marfikus/3d-kinematics/3d_models/parts/table_2_stepper_holder.SLDPRT

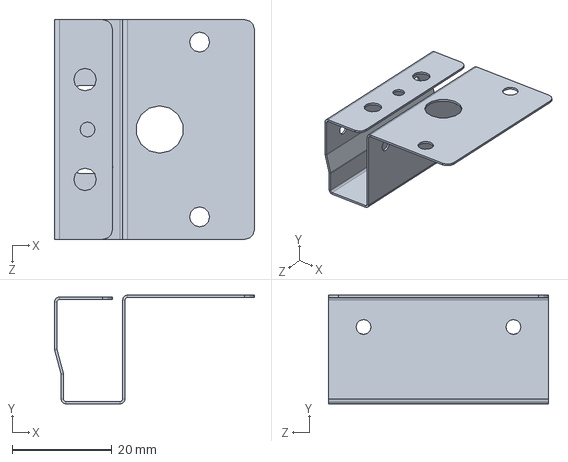
[picture p17: CAD file, 2021-09-27]
3d_models/parts/table_2_stepper_holder.SLDPRT
40.1 x 21.8 x 44.0 mm
