marfikus/3d-kinematics/3d_models/parts/z_axis_side_support.SLDPRT

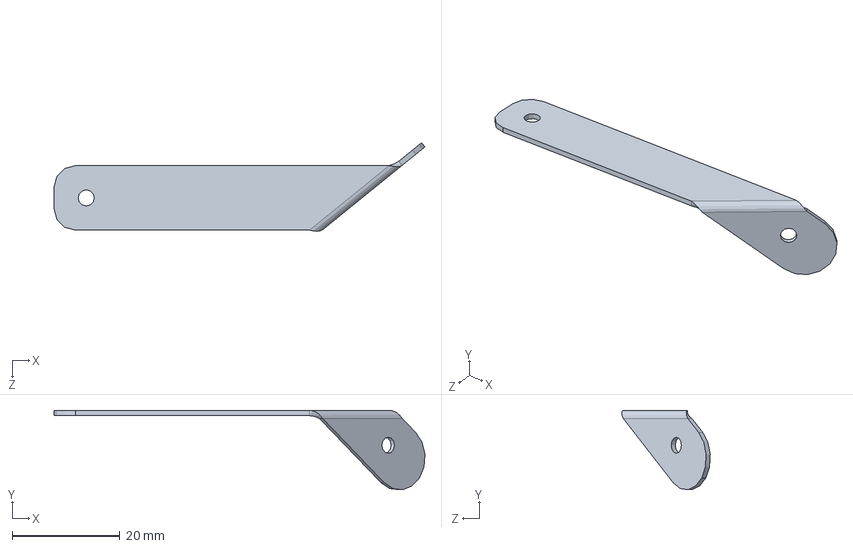
[picture p18: CAD file, 2021-09-27]
3d_models/parts/z_axis_side_support.SLDPRT
69.0 x 14.8 x 16.5 mm
