marfikus/3d-kinematics/3d_models/parts/table_2_stepper_rail_support_right.SLDPRT

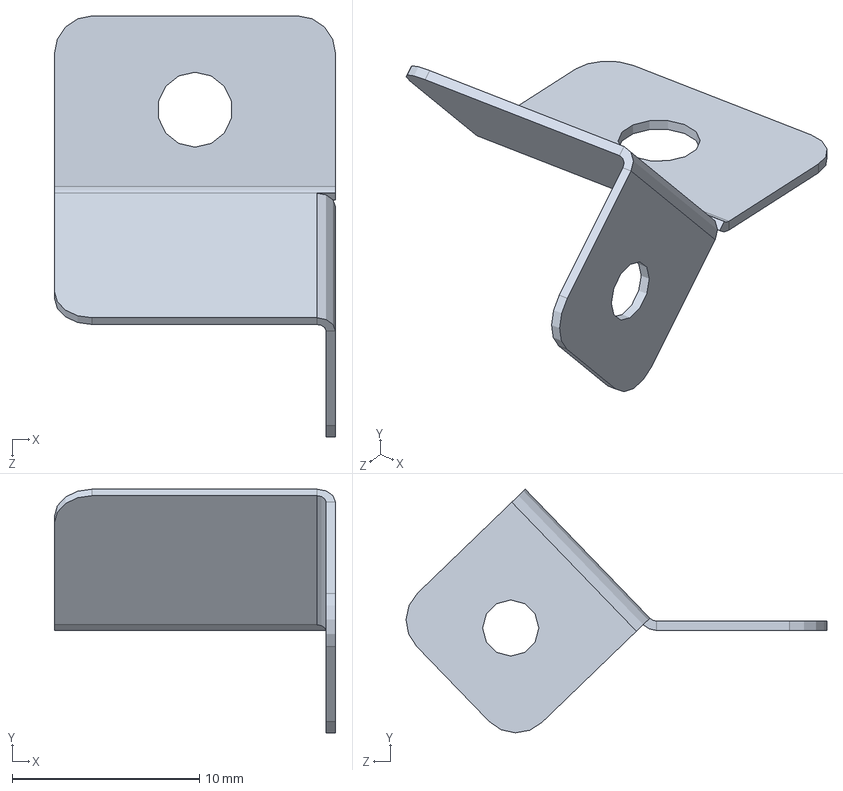
[picture p19: CAD file, 2021-09-27]
3d_models/parts/table_2_stepper_rail_support_right.SLDPRT
15.0 x 13.0 x 22.5 mm
