marfikus/3d-kinematics/3d_models/parts/table_1_stepper_holder.SLDPRT

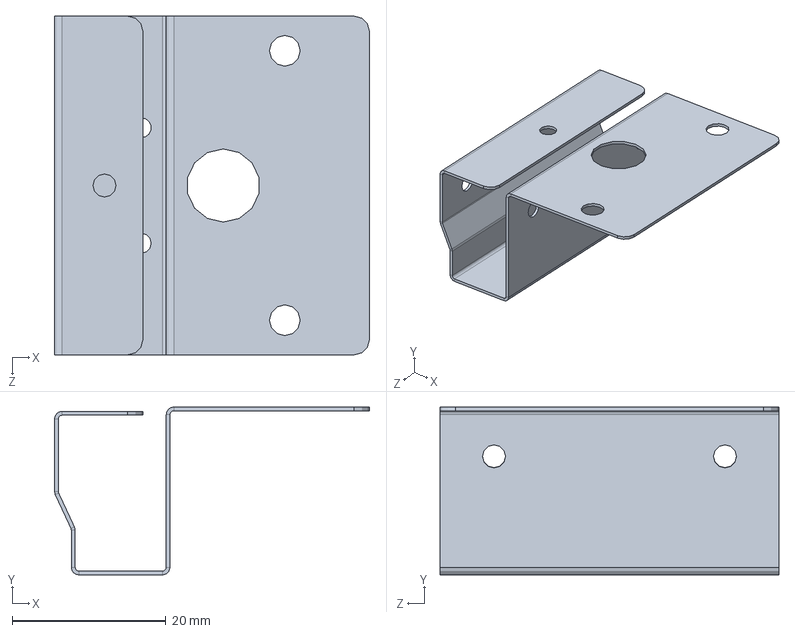
[picture p20: CAD file, 2021-09-27]
3d_models/parts/table_1_stepper_holder.SLDPRT
40.9 x 21.8 x 44.0 mm
