marfikus/3d-kinematics/3d_models/parts/z_axis_stepper_holder.SLDPRT

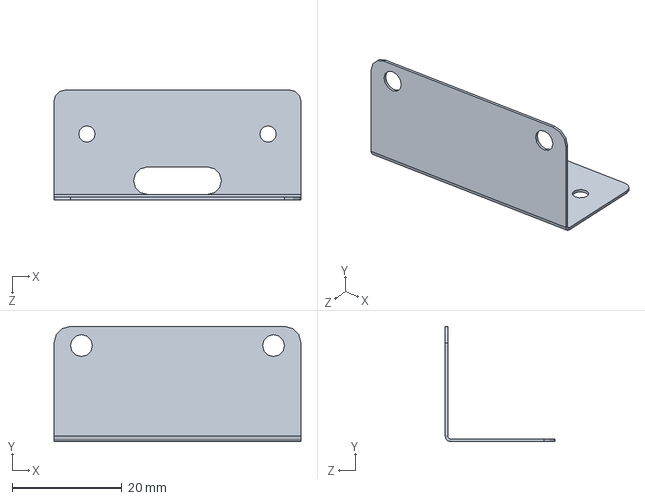
[picture p21: CAD file, 2021-09-27]
3d_models/parts/z_axis_stepper_holder.SLDPRT
45.0 x 21.0 x 20.0 mm
