marfikus/3d-kinematics/3d_models/parts/z_axis_rails_holder_1_2.SLDPRT

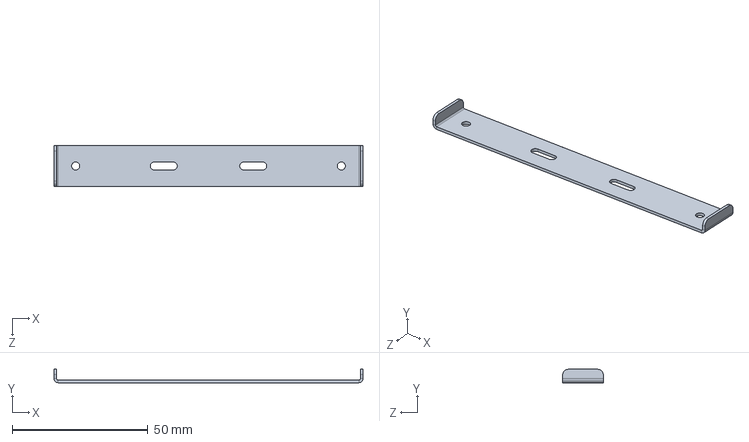
[picture p22: CAD file, 2021-09-27]
3d_models/parts/z_axis_rails_holder_1_2.SLDPRT
114.0 x 5.00 x 15.0 mm
