marfikus/3d-kinematics/3d_models/parts/table_support_1.SLDPRT

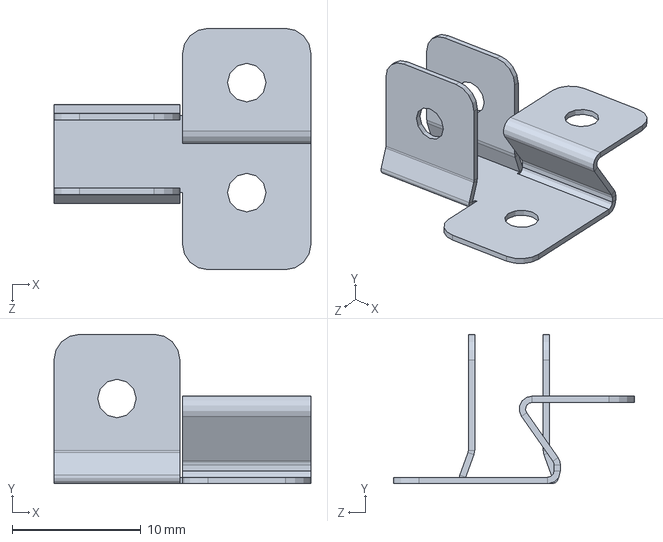
[picture p23: CAD file, 2021-09-24]
3d_models/parts/table_support_1.SLDPRT
20.0 x 11.6 x 18.8 mm
