marfikus/3d-kinematics/3d_models/parts/table_1_rail_support.SLDPRT

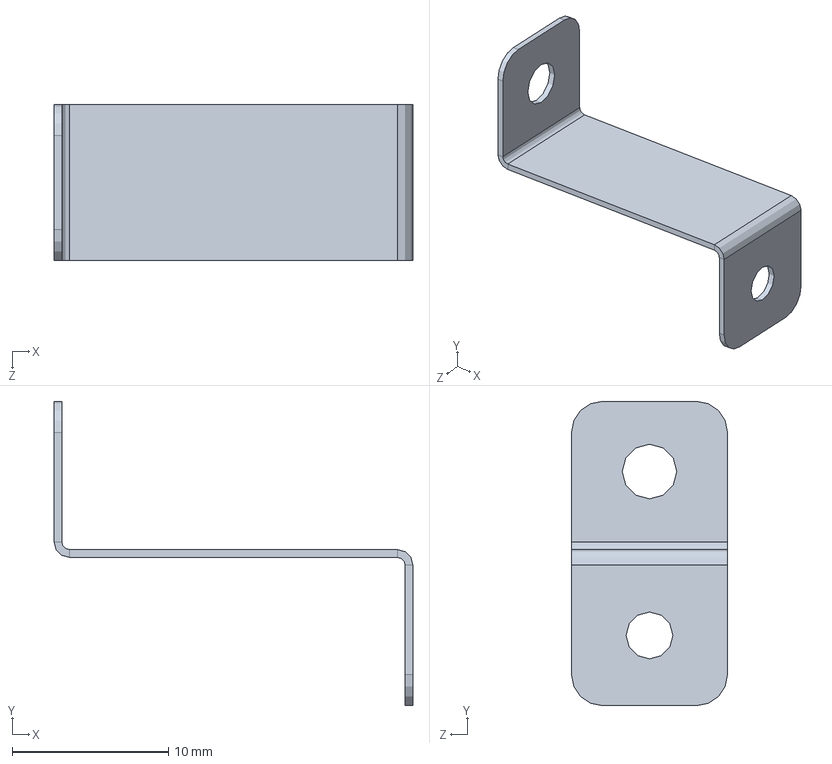
[picture p24: CAD file, 2021-09-24]
3d_models/parts/table_1_rail_support.SLDPRT
23.0 x 19.5 x 10.0 mm
