marfikus/3d-kinematics/3d_models/parts/table_1.SLDPRT

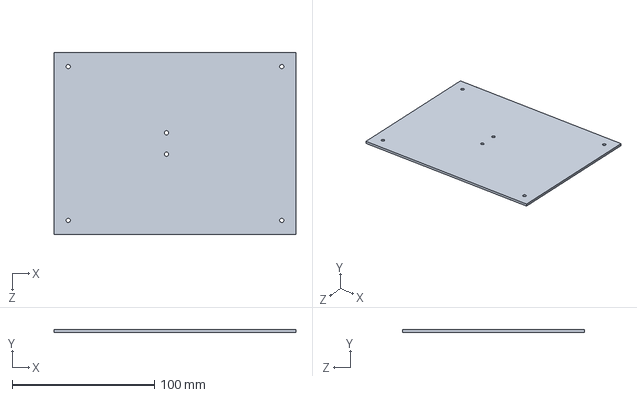
[picture p25: CAD file, 2021-09-24]
3d_models/parts/table_1.SLDPRT
170.0 x 2.00 x 128.0 mm
