marfikus/3d-kinematics/3d_models/parts/table_1_stepper_rail_support.SLDPRT

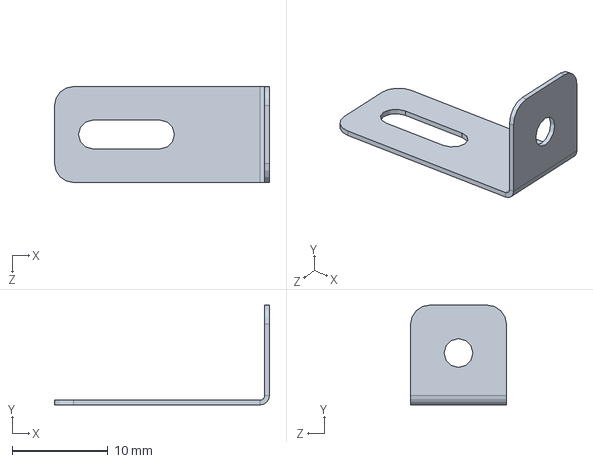
[picture p26: CAD file, 2021-09-24]
3d_models/parts/table_1_stepper_rail_support.SLDPRT
22.4 x 10.4 x 10.0 mm
