marfikus/3d-kinematics/3d_models/parts/table_support_2.SLDPRT

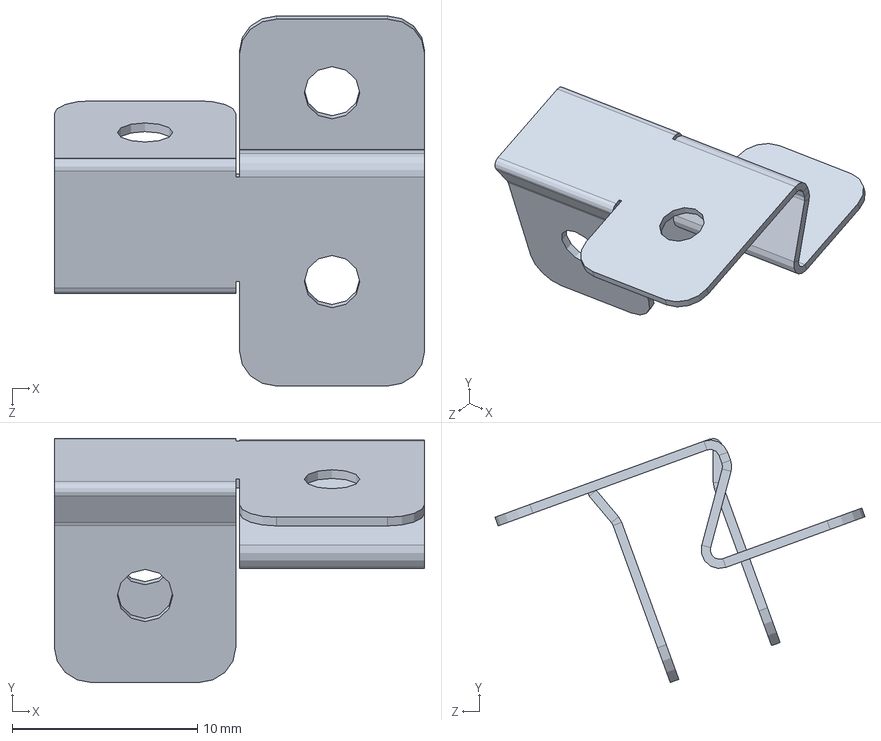
[picture p27: CAD file, 2021-09-24]
3d_models/parts/table_support_2.SLDPRT
20.0 x 13.2 x 20.0 mm
