marfikus/3d-kinematics/3d_models/parts/z_axis_rack_bracing_1_1.SLDPRT

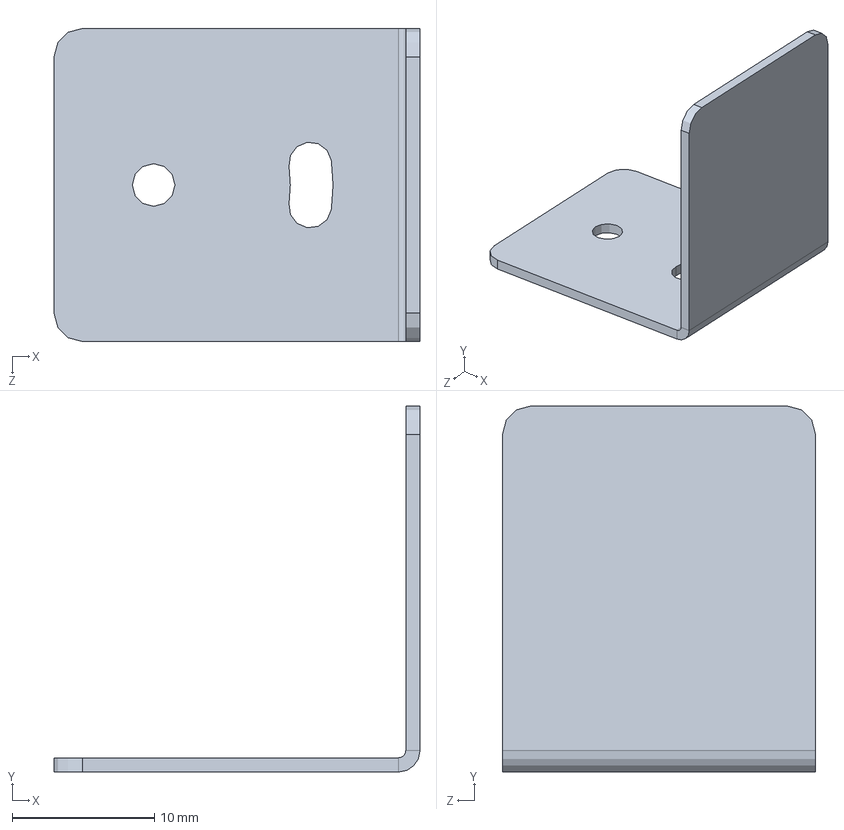
[picture p28: CAD file, 2021-09-23]
3d_models/parts/z_axis_rack_bracing_1_1.SLDPRT
25.7 x 25.7 x 22.0 mm
