marfikus/3d-kinematics/3d_models/parts/z_axis_rack_bracing_1_2.SLDPRT

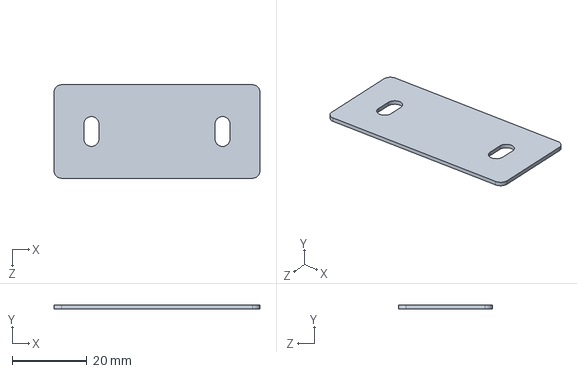
[picture p29: CAD file, 2021-09-23]
3d_models/parts/z_axis_rack_bracing_1_2.SLDPRT
55.0 x 1.00 x 25.0 mm
