marfikus/3d-kinematics/3d_models/parts/z_axis_upper_corner.SLDPRT

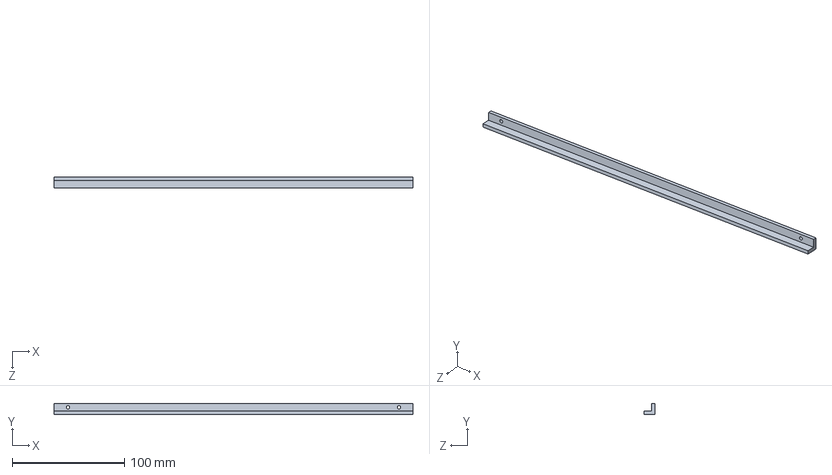
[picture p30: CAD file, 2021-09-23]
3d_models/parts/z_axis_upper_corner.SLDPRT
320.0 x 10.0 x 10.0 mm
