marfikus/3d-kinematics/3d_models/parts/base.SLDPRT

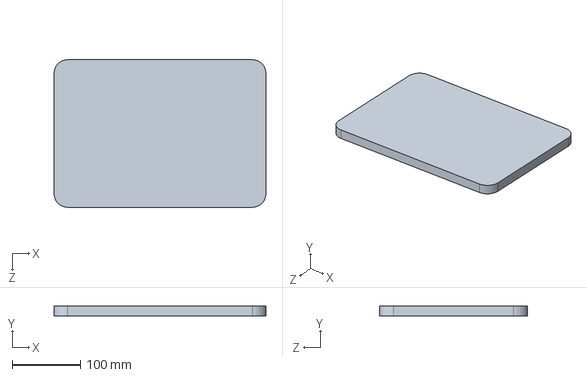
[picture p31: CAD file, 2021-09-21]
3d_models/parts/base.SLDPRT
310.0 x 15.0 x 216.0 mm
