marfikus/3d-kinematics/3d_models/parts/corner_rail_2.SLDPRT

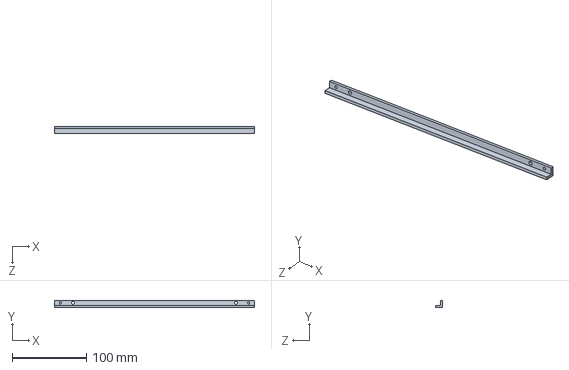
[picture p32: CAD file, 2021-09-21]
3d_models/parts/corner_rail_2.SLDPRT
270.0 x 10.0 x 10.0 mm
