marfikus/3d-kinematics/3d_models/parts/corner_rail_3.SLDPRT

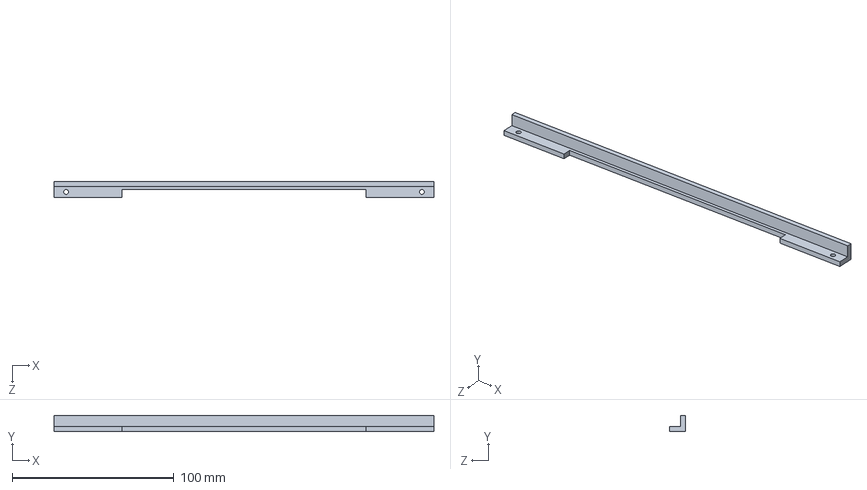
[picture p33: CAD file, 2021-09-21]
3d_models/parts/corner_rail_3.SLDPRT
235.0 x 10.0 x 10.0 mm
