marfikus/3d-kinematics/3d_models/parts/short_roller.SLDPRT

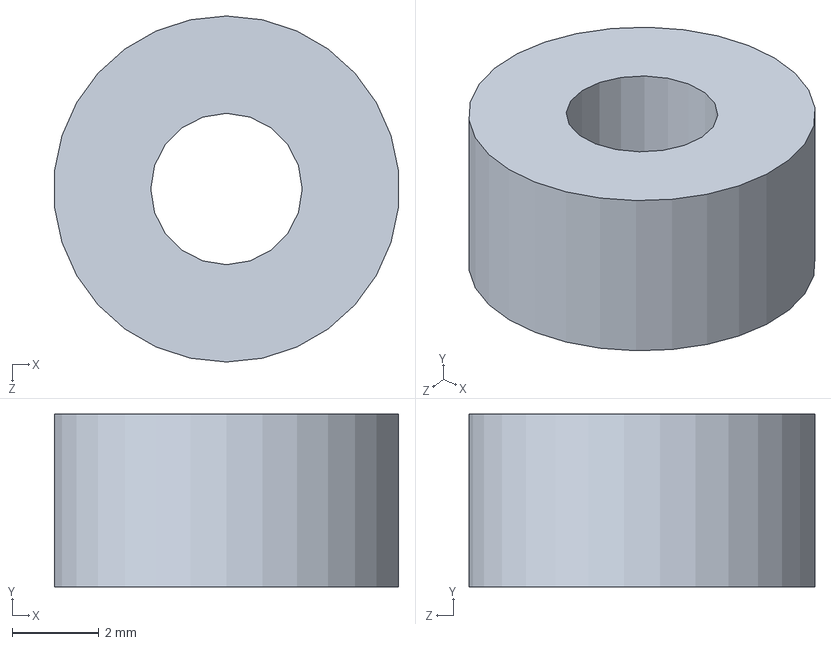
[picture p34: CAD file, 2021-09-21]
3d_models/parts/short_roller.SLDPRT
7.96 x 4.00 x 8.00 mm
