marfikus/3d-kinematics/3d_models/parts/long_roller.SLDPRT

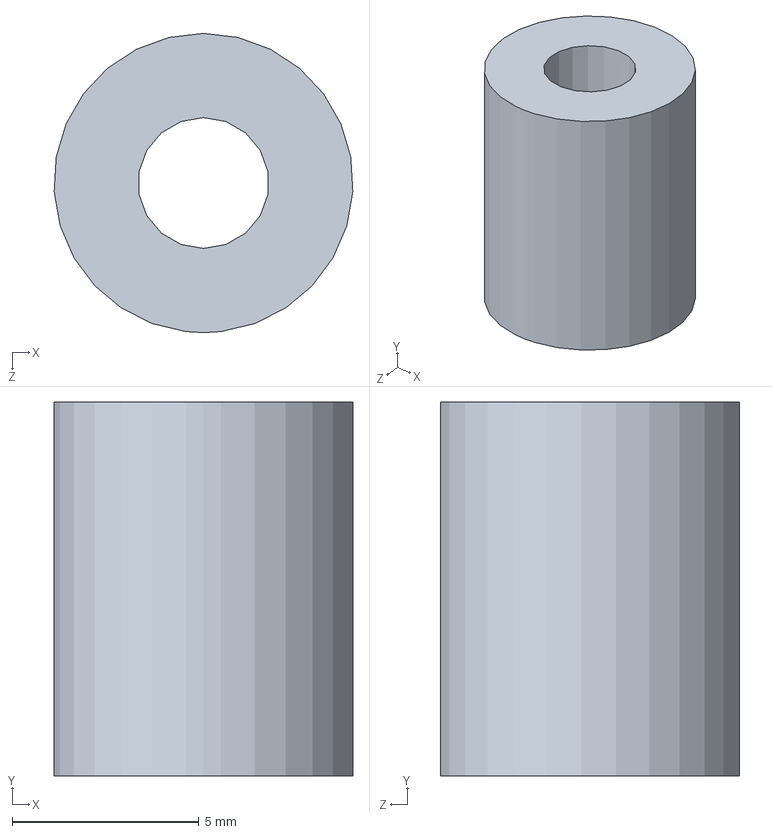
[picture p35: CAD file, 2021-09-21]
3d_models/parts/long_roller.SLDPRT
7.99 x 10.0 x 8.00 mm
