marfikus/3d-kinematics/3d_models/parts/table_2_stepper_support.SLDPRT

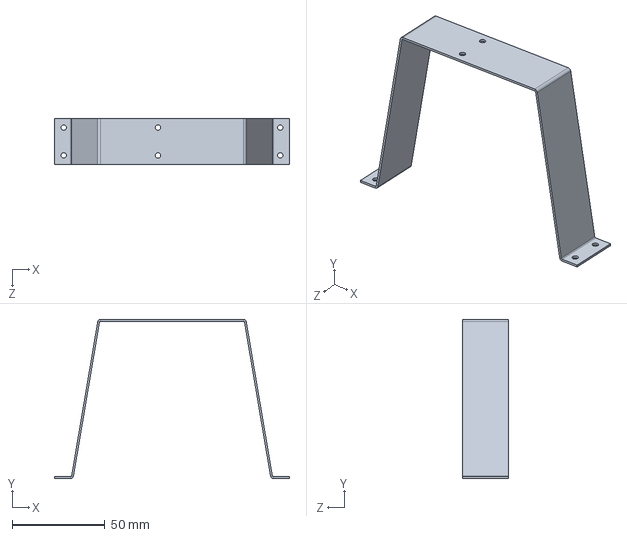
[picture p36: CAD file, 2021-09-21]
3d_models/parts/table_2_stepper_support.SLDPRT
126.7 x 85.8 x 25.0 mm
