marfikus/3d-kinematics/3d_models/parts/z_axis_rails_holder_1_1.SLDPRT

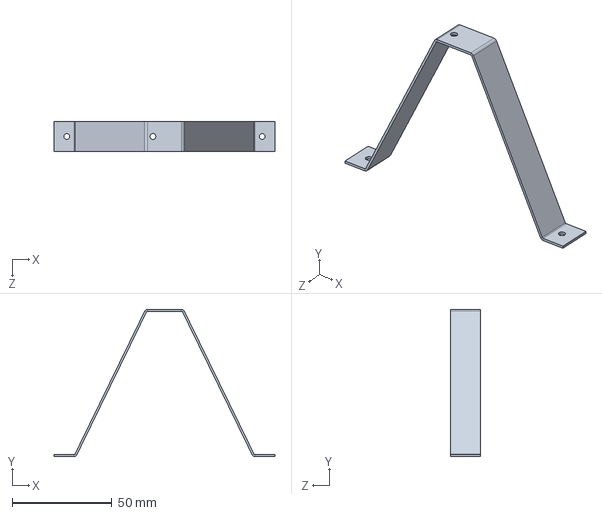
[picture p37: CAD file, 2021-09-21]
3d_models/parts/z_axis_rails_holder_1_1.SLDPRT
110.7 x 73.7 x 15.0 mm
