marfikus/3d-kinematics/3d_models/parts/stepper.SLDPRT

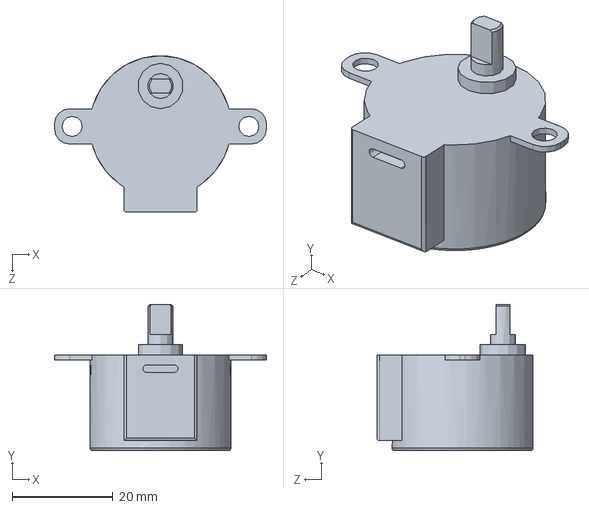
[picture p38: CAD file, 2021-09-21]
3d_models/parts/stepper.SLDPRT
42.0 x 29.0 x 31.0 mm
