marfikus/3d-kinematics/3d_models/parts/gear_imitation.SLDPRT

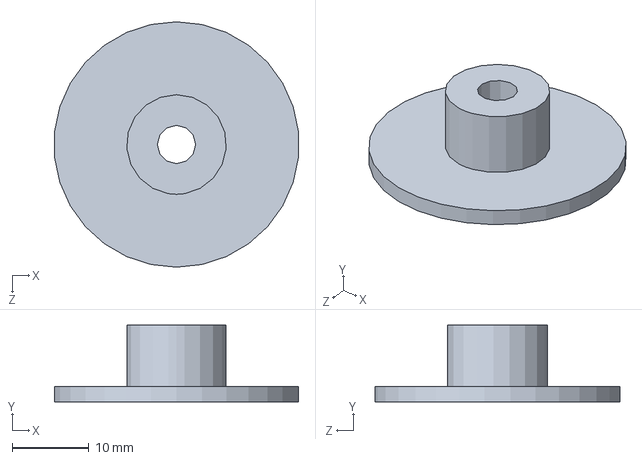
[picture p39: CAD file, 2021-09-21]
3d_models/parts/gear_imitation.SLDPRT
31.8 x 10.0 x 32.0 mm
