marfikus/3d-kinematics/3d_models/parts/rubberized_roller.SLDPRT

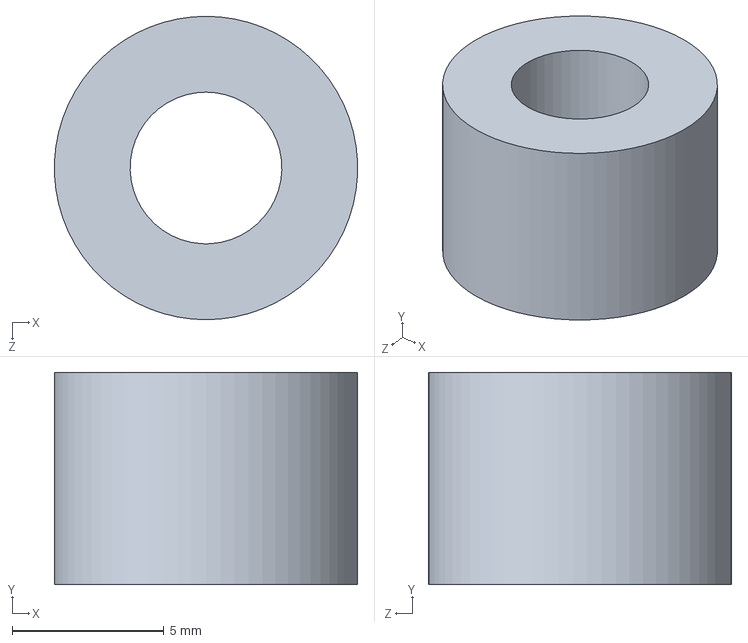
[picture p40: CAD file, 2021-09-21]
3d_models/parts/rubberized_roller.SLDPRT
9.99 x 7.00 x 10.0 mm
