marfikus/3d-kinematics/3d_models/parts/toothed_rail_imitation.SLDPRT

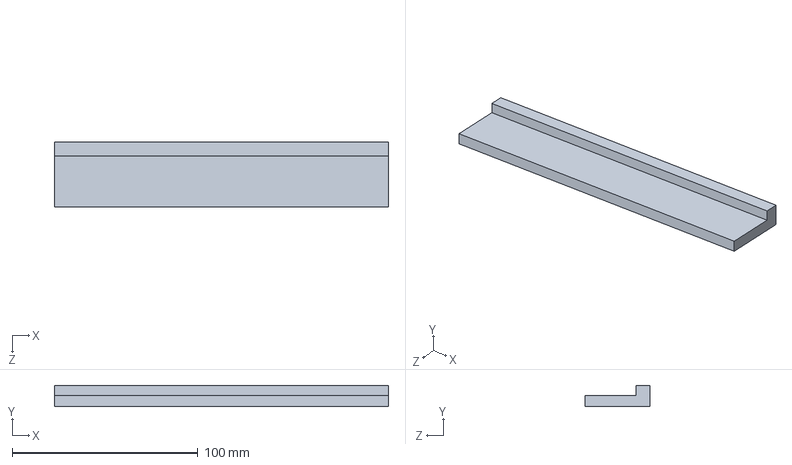
[picture p41: CAD file, 2021-09-21]
3d_models/parts/toothed_rail_imitation.SLDPRT
180.0 x 11.5 x 35.0 mm
